EDrTech/PMG001/docs/visual/breakout_pmg001_bottom.png

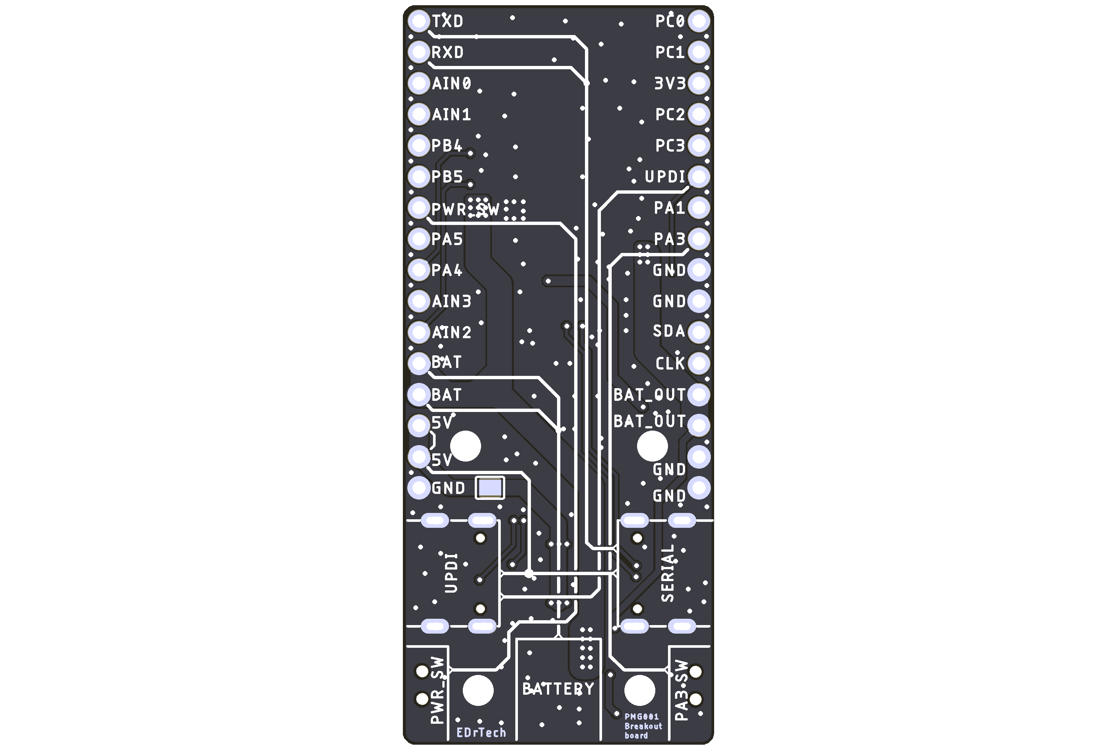
docs/visual/breakout_pmg001_bottom.png
