EDrTech/PMG001/docs/visual/breakout_pmg001_cover_board_top.png

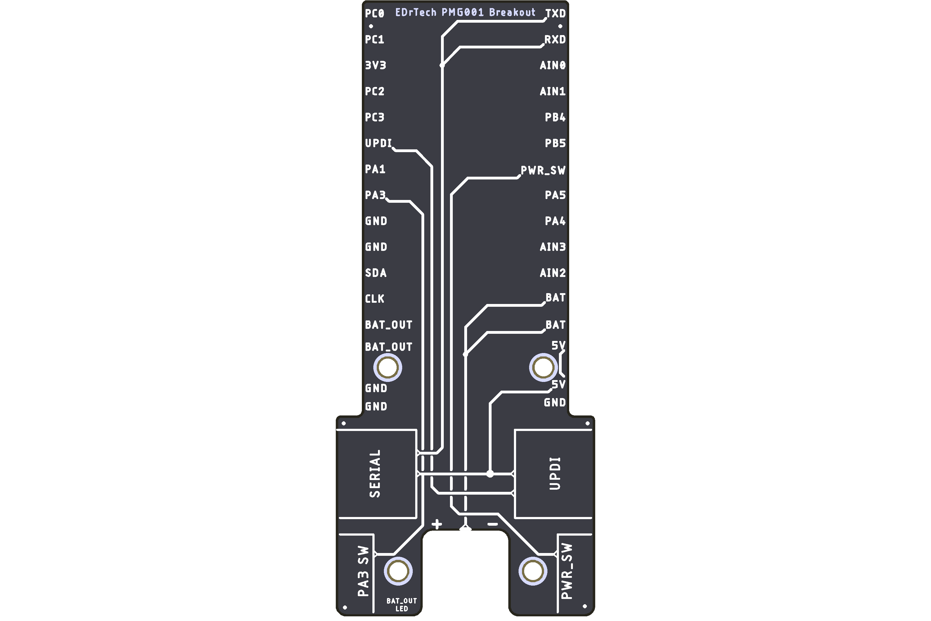
docs/visual/breakout_pmg001_cover_board_top.png
