EDrTech/PMG001/docs/visual/df_fin.png

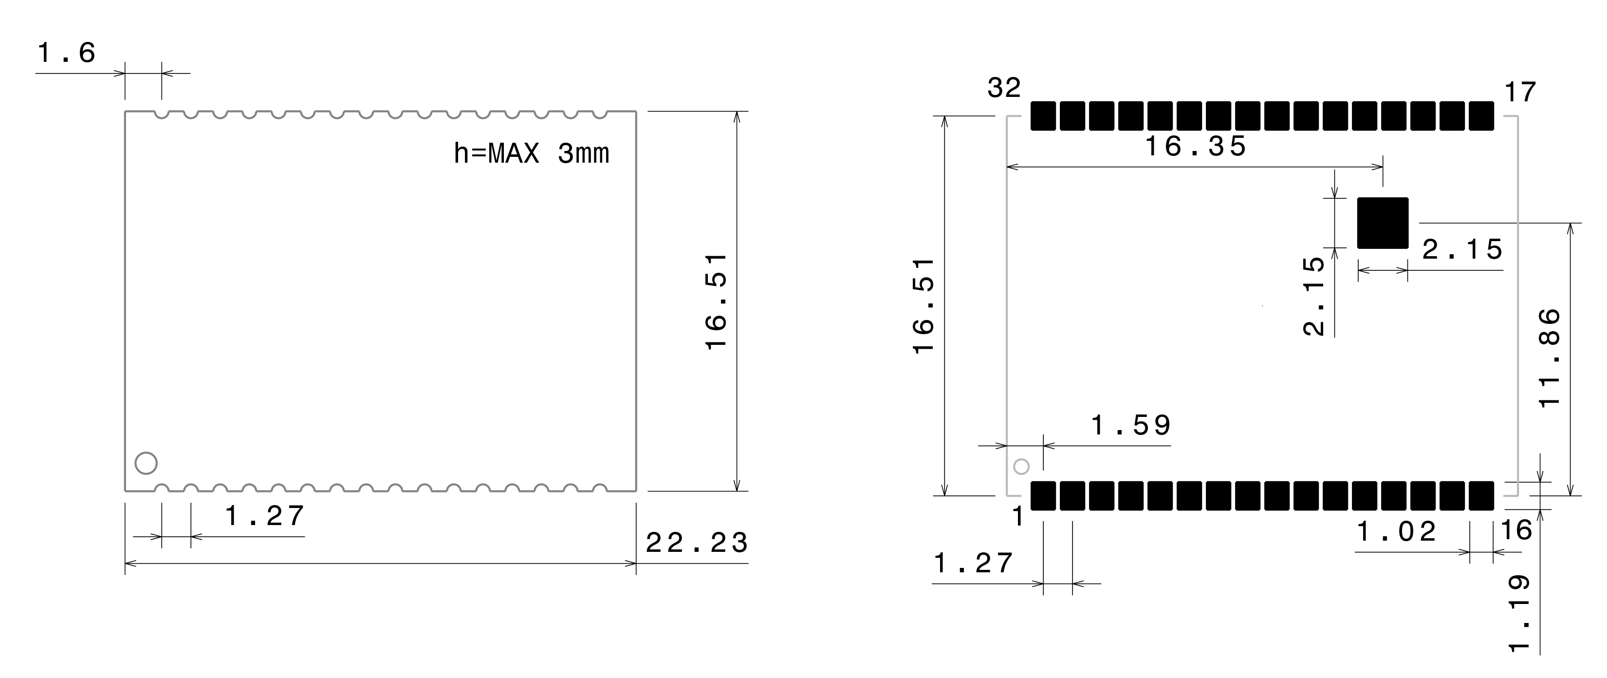
docs/visual/df_fin.png
