EDrTech/PMG001/docs/visual/pmg001_bottom.png

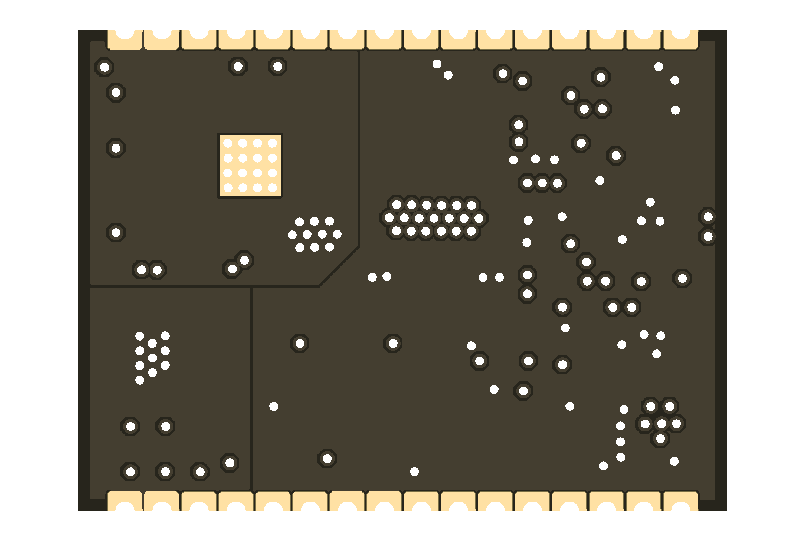
docs/visual/pmg001_bottom.png
