EDrTech/PMG001/docs/visual/resistor_divider.png

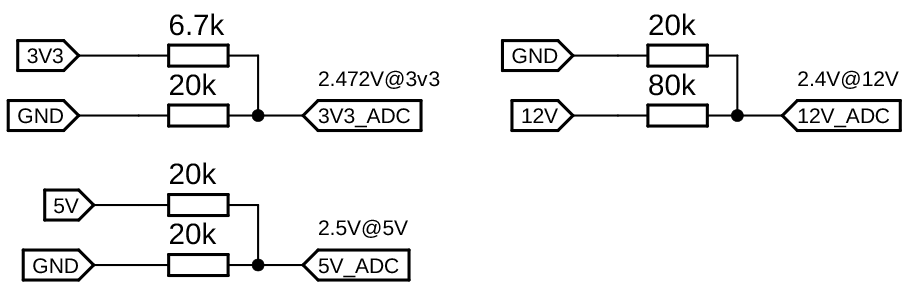
docs/visual/resistor_divider.png
